RBEGamer/NixieClock/documenation/pictures/ctrl_schem.png

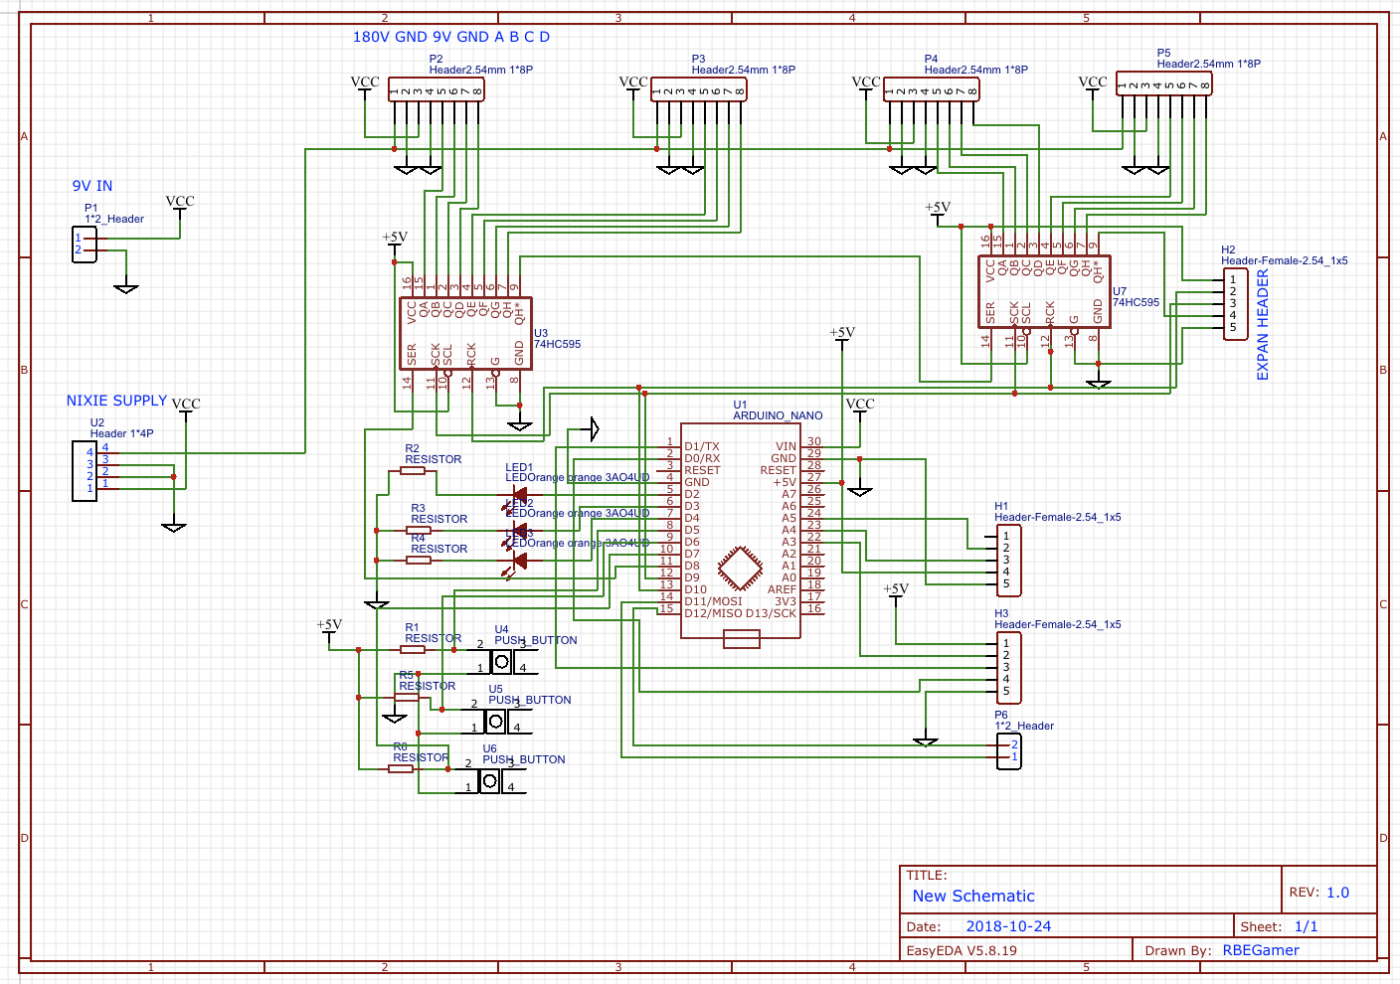
documenation/pictures/ctrl_schem.png
