RBEGamer/NixieClock/documenation/pictures/in8_pcb.png

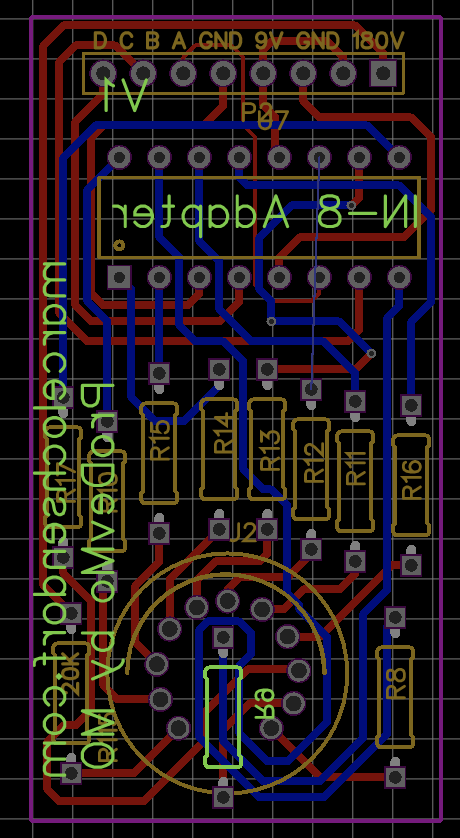
documenation/pictures/in8_pcb.png
