RBEGamer/NixieClock/documenation/pictures/in16_schem.png

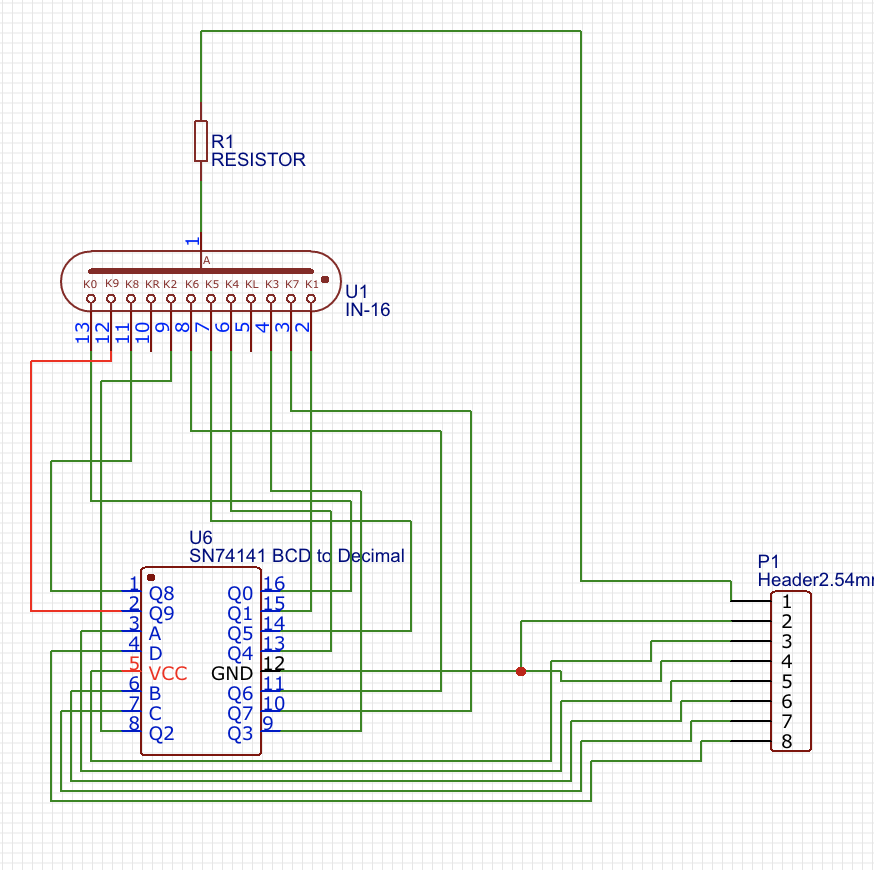
documenation/pictures/in16_schem.png
