RBEGamer/NixieClock/documenation/pictures/nixie_fin_3.JPG

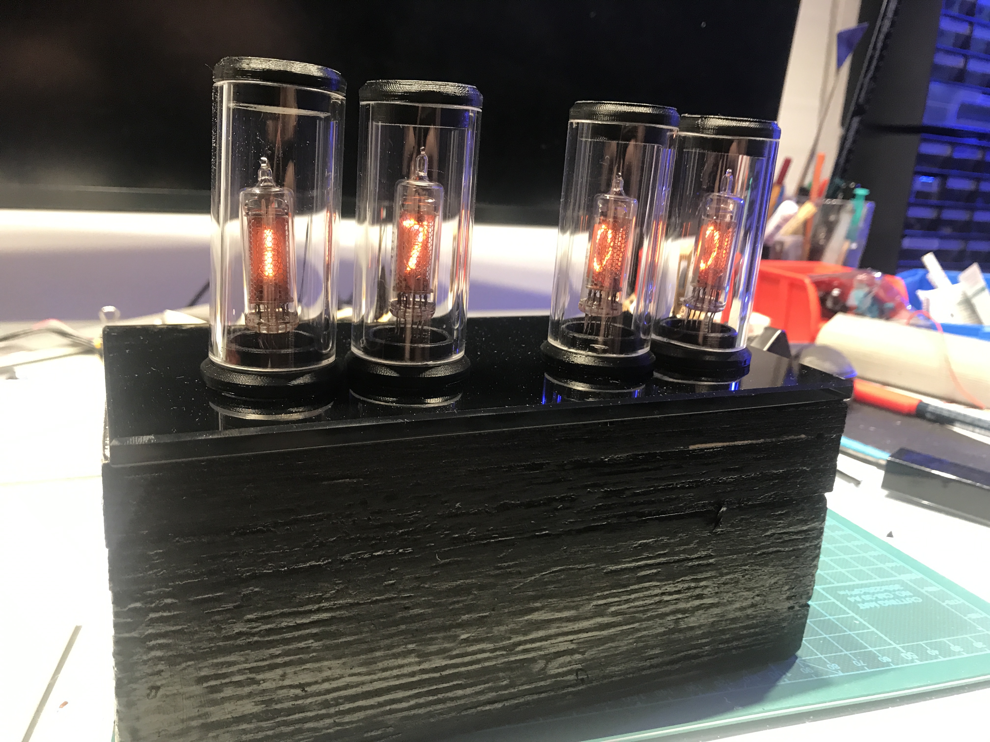
documenation/pictures/nixie_fin_3.JPG
