RBEGamer/NixieClock/documenation/pictures/nxie_fin_1.JPG

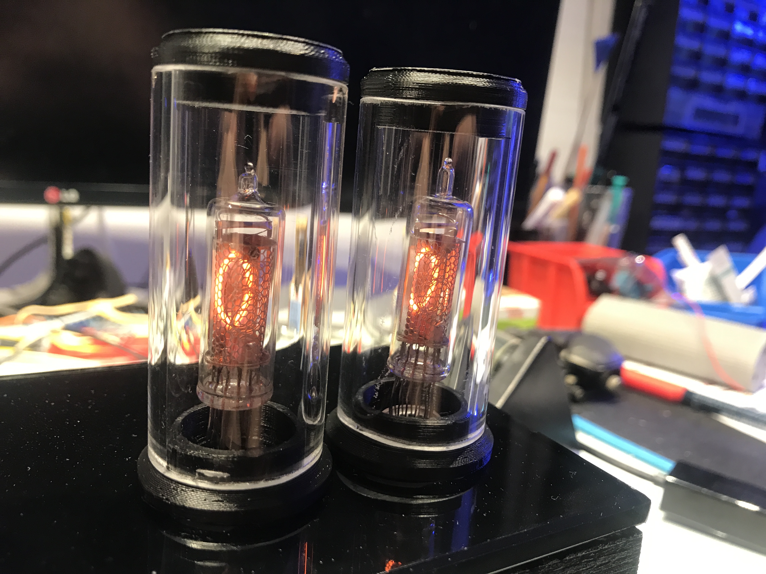
documenation/pictures/nxie_fin_1.JPG
