RBEGamer/NixieClock/documenation/pictures_build/box_1.jpg

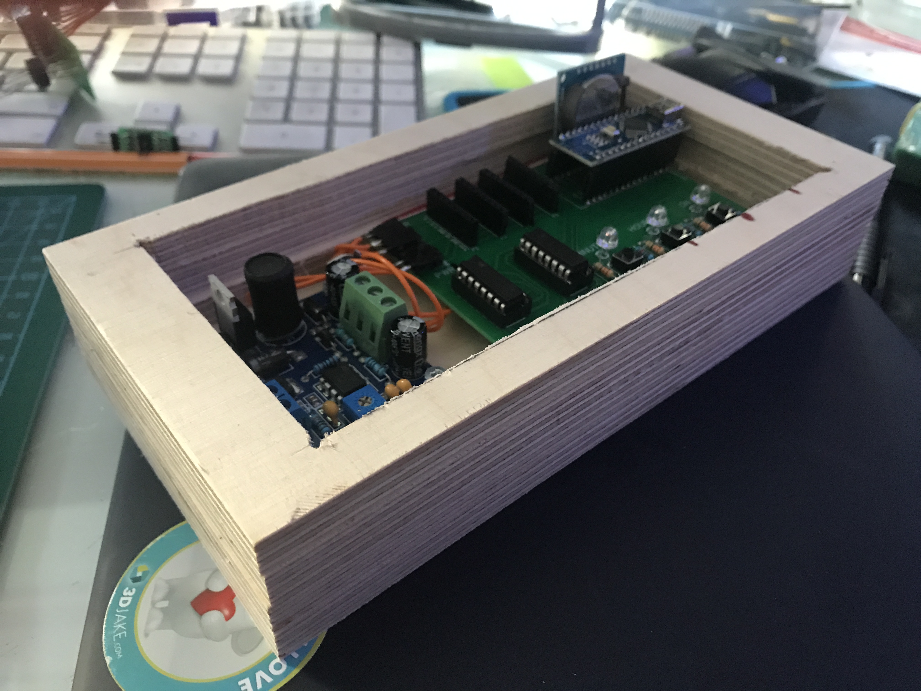
documenation/pictures_build/box_1.jpg
