RBEGamer/NixieClock/documenation/pictures_build/glass_plate.jpg

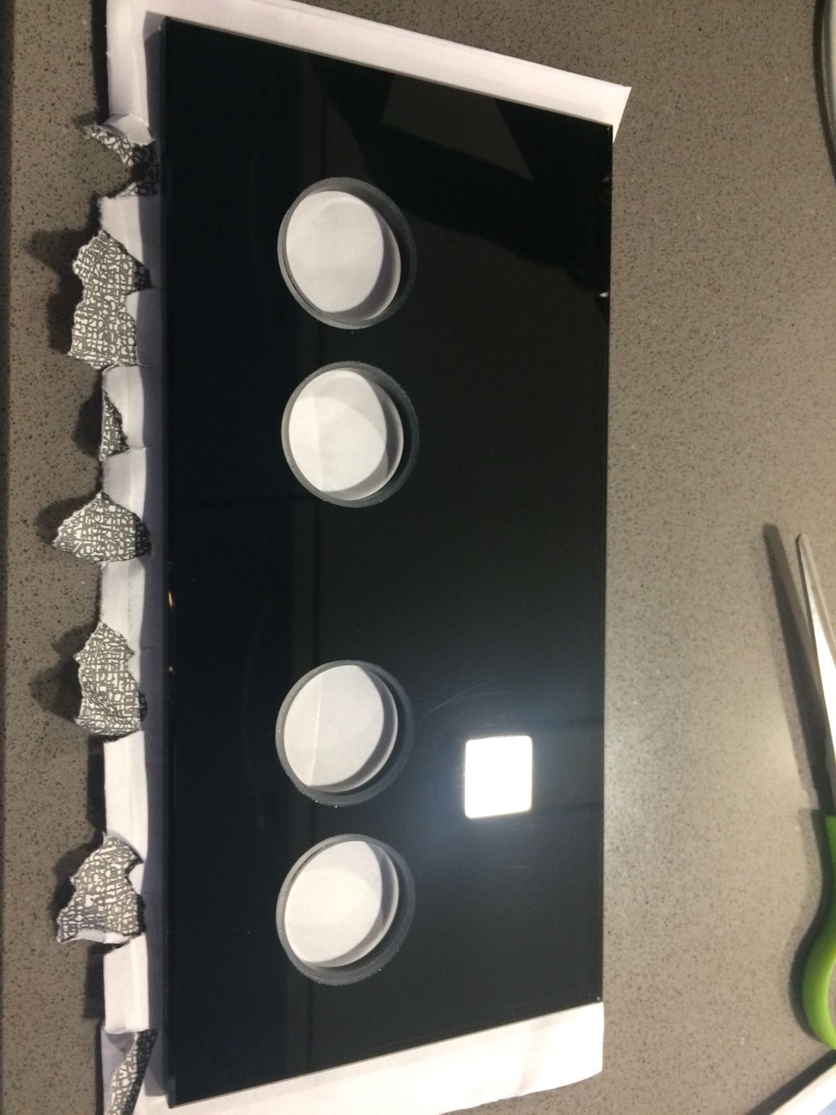
documenation/pictures_build/glass_plate.jpg
